khoifrvn/Left-hand-trackball-with-Adafruit-ANO-Encoder/Picture/IMG_0205.jpeg

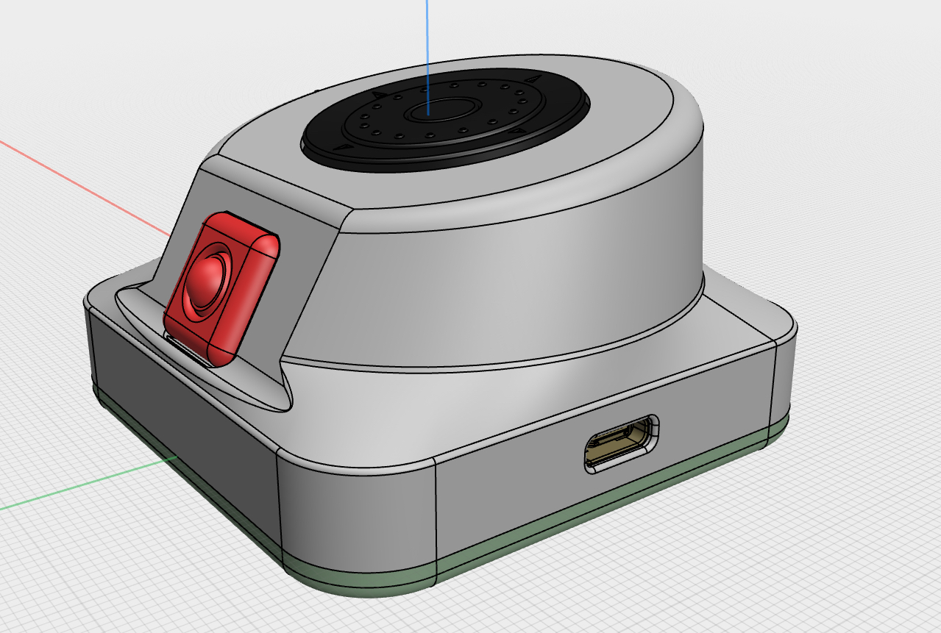
Picture/IMG_0205.jpeg
