khoifrvn/Left-hand-trackball-with-Adafruit-ANO-Encoder/Picture/IMG_0206.jpeg

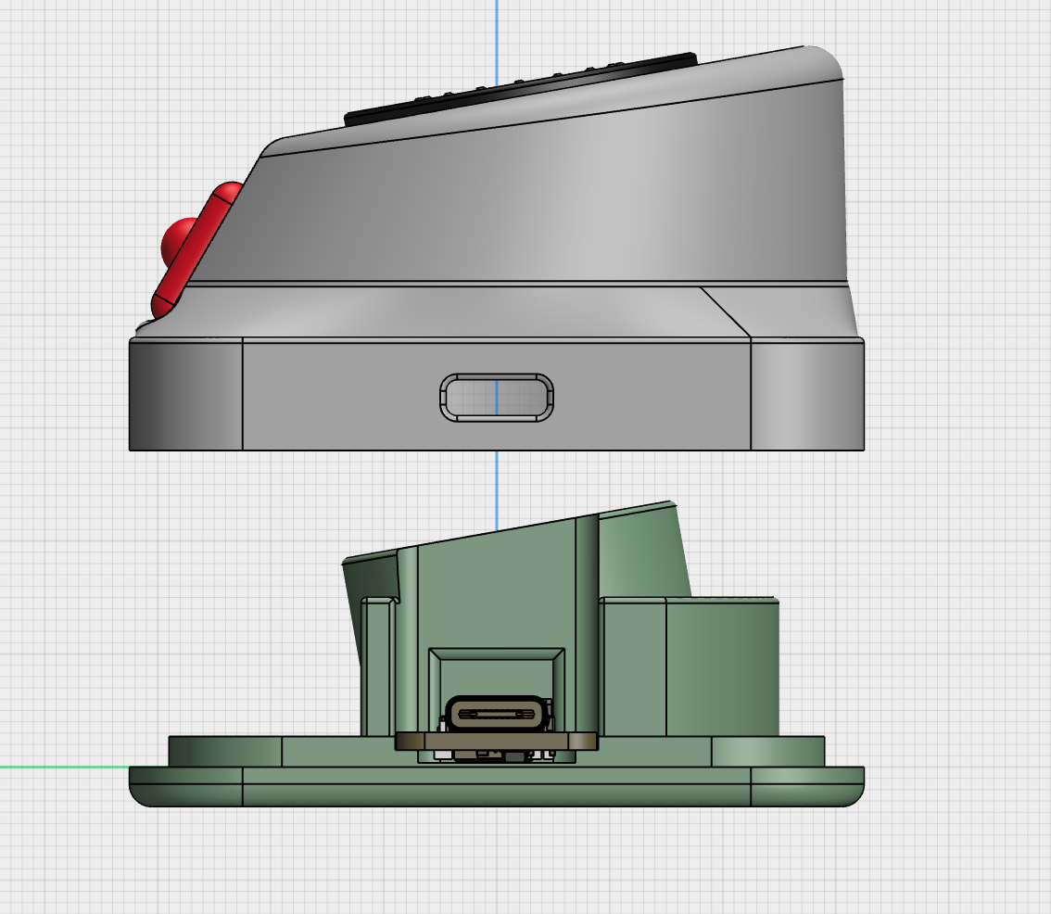
Picture/IMG_0206.jpeg
