khoifrvn/Left-hand-trackball-with-Adafruit-ANO-Encoder/Picture/IMG_0207.jpeg

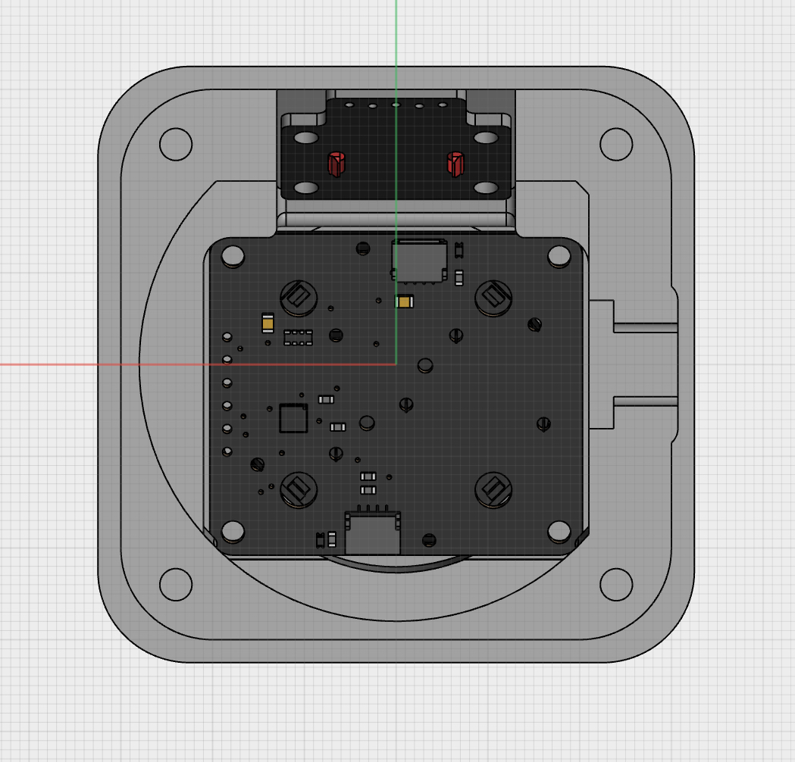
Picture/IMG_0207.jpeg
